jdavidguerrero/grooveforge-brain/apps/docs/sprints/37-auto-harmonization.md

# Sprint 37 — Auto-Harmonization

> **Fase:** 6 — Layer 1 AI completo
> **Sprint del roadmap:** 6.2
> **Estimado:** 3-4 sesiones (~10-14h)
> **Status:** 🟡 In Progress (Theory escrita, código pendiente)
> **Refs:** `apps/docs/06-implementation-roadmap.md §6.2` · `apps/docs/04-ai-architecture.md §1.3`

---

## Theory

### Concepto central

Imaginate que estás tocando en un grupo y hay un segundo músico que te sigue en silencio.
No necesita verte ni escucharte en detalle — solo sabe en qué tonalidad están tocando.
Con eso le alcanza para saber exactamente qué nota tocar junto a la tuya, siempre en
escala, siempre armónica. Eso es la armonización diatónica: **una función que, dada una
nota y una tonalidad, devuelve la nota que un segundo músico competente tocaría encima
sin pensar dos veces**.

En términos técnicos: el GrooveForge Brain ya conoce la tonalidad (el KeyDetector,
Sprint 4.3, 94% de accuracy). El único paso adicional es calcular, para cada nota MIDI
que llega, qué nota de la misma escala está a una tercera o sexta diatónica de distancia.
Ese cálculo es una búsqueda lineal en 7 elementos más una suma — no hay inferencia, no
hay tensor arena, no hay modelo. Es **teoría musical pura convertida en código determinístico**.

El resultado audible: tocás una nota → escuchás dos voces sonando juntas, ambas en escala,
siempre consonantes. Para un músico inexperto, suena como "tocar bien" de forma automática.
Para un músico experimentado, es un segundo color armónico instantáneo.

---

### Por qué lo hacemos así

La pregunta de diseño central es: ¿la armonización debería ser un modelo de ML o una
función determinística?

| Approach | Ventaja | Desventaja | Decisión |
|---|---|---|---|
| Tabla de intervalos diatónicos (determinístico) | Sin training, sin arena tensor, <1 µs CPU, 100% predecible musicalmente, fácil de debuggear | No aprende preferencias del usuario | ✅ Elegido para v1 |
| Modelo TFLite que elige el intervalo | Puede aprender qué intervalos suenan mejor en contexto | Requiere dataset de decisiones armónicas, 8-20ms inferencia, arena RAM, result a veces no-obvio | ❌ Descartado para v1 |
| Voice-leading completo (resolver acordes) | Resultado más "orquestal" | Complejidad O(voces²), latencia multi-ms, fuera del scope de un synth en vivo | ❌ Fuera de scope |

**La tabla de intervalos es completamente determinística dado el tipo de escala.** El ML
ya hizo su trabajo en el Sprint 4.3 (detectar la tonalidad). A partir de ahí, la
armonización es matemática: cada grado de la escala tiene un intervalo de tercera y de
sexta perfectamente definido por la teoría musical occidental. No hay ambigüedad, no hay
entrenamiento necesario.

Esto no es una limitación — es la decisión correcta. La armonización diatónica lleva
siglos siendo determinística. Los músicos del Renacimiento ya conocían exactamente las
mismas tablas que estamos implementando. El ML agrega valor cuando el problema es
estadístico o depende del contexto. Aquí el problema es algebraico.

---

### Cómo funciona (más profundo)

#### Las escalas diatónicas tienen 7 grados, cada uno con su tercera fija

Una escala mayor (modo jónico) o menor natural (modo eólico) tiene exactamente 7 notas.
Cada nota ocupa un **grado** en la escala, numerado del 1 al 7. La relación entre un grado
y su tercera diatónica (dos grados arriba) está fijada por la estructura de la escala —
no cambia según el contexto armónico del momento.

Para calcular la nota de armonía, el algoritmo hace tres pasos:

```
1. Encontrar el grado de la nota tocada dentro de la escala.
2. Consultar la tabla: ese grado → cuántos semitonos sube la armonía.
3. Calcular: harmony_note = midi_note + semitones_from_table[degree]
```

El paso 1 es una búsqueda lineal en un array de 7 elementos (los pitch classes de la
escala activa). El paso 2 es un acceso a array en tiempo constante. El paso 3 es una
suma. Todo el proceso corre en menos de 1 µs en el Cortex-M7 del Teensy 4.1.

#### Tabla de intervalos para escala mayor (modo jónico)

Cada fila es un grado de la escala. La columna "semitones" indica cuántos semitonos hay
que sumarle a la nota original para obtener la tercera diatónica.

| Grado | Nota (en C maj) | Tercera diatónica | Tipo de tercera | Semitonos |
|---|---|---|---|---|
| 1 | C | E | Mayor | +4 |
| 2 | D | F | Menor | +3 |
| 3 | E | G | Menor | +3 |
| 4 | F | A | Mayor | +4 |
| 5 | G | B | Mayor | +4 |
| 6 | A | C | Menor | +3 |
| 7 | B | D | Menor | +3 |

Array en C++: `constexpr int8_t MAJOR_THIRDS[] = {4, 3, 3, 4, 4, 3, 3};`

La suma de ese array es 24 — exactamente 2 octavas, lo que confirma que la tabla "cierra"
correctamente al volver al grado 1 una octava más arriba.

Para la **sexta diatónica** (cuatro grados arriba, que es la inversión de la tercera):

| Grado | Nota (en C maj) | Sexta diatónica | Tipo | Semitonos |
|---|---|---|---|---|
| 1 | C | A | Mayor | +9 |
| 2 | D | B | Mayor | +9 |
| 3 | E | C | Menor | +8 |
| 4 | F | D | Mayor | +9 |
| 5 | G | E | Mayor | +9 |
| 6 | A | F | Menor | +8 |
| 7 | B | G | Menor | +8 |

Array: `constexpr int8_t MAJOR_SIXTHS[] = {9, 9, 8, 9, 9, 8, 8};`

#### Tabla de intervalos para escala menor natural (modo eólico)

La escala menor natural tiene una distribución de semitonos distinta: `[0, 2, 3, 5, 7, 8, 10]`.
Esto cambia qué terceras son mayores y cuáles son menores:

| Grado | Nota (en A min) | Tercera diatónica | Tipo | Semitonos |
|---|---|---|---|---|
| 1 | A | C | Menor | +3 |
| 2 | B | D | Menor | +3 |
| 3 | C | E | Mayor | +4 |
| 4 | D | F | Menor | +3 |
| 5 | E | G | Menor | +3 |
| 6 | F | A | Mayor | +4 |
| 7 | G | B | Mayor | +4 |

Array: `constexpr int8_t MINOR_THIRDS[] = {3, 3, 4, 3, 3, 4, 4};`

Para la **sexta diatónica menor natural**:

| Grado | Nota (en A min) | Sexta diatónica | Tipo | Semitonos |
|---|---|---|---|---|
| 1 | A | F | Menor | +8 |
| 2 | B | G | Menor | +8 |
| 3 | C | A | Mayor | +9 |
| 4 | D | B | Menor | +8 |
| 5 | E | C | Menor | +8 |
| 6 | F | D | Mayor | +9 |
| 7 | G | E | Mayor | +9 |

Array: `constexpr int8_t MINOR_SIXTHS[] = {8, 8, 9, 8, 8, 9, 9};`

**Verificación de integridad:** la suma de MINOR_THIRDS es también 24 (2 octavas). La
suma de los sixths, tanto para mayor como para menor, suma a 60 (5 octavas), lo que
también cierra correctamente.

#### Cómo encontrar el grado de una nota

Dado un `midi_note` y un array `scale_notes[7]` de pitch classes (ya provisto por
`ScaleLock::get_scale_notes()`):

```cpp
uint8_t pitch_class = midi_note % 12;
int degree = -1;
for (int i = 0; i < 7; i++) {
    if (scale_notes[i] == pitch_class) {
        degree = i;  // índice 0-6, que corresponde a grado 1-7
        break;
    }
}
// Si degree == -1: la nota no está en la escala → no armonizar, retornar 0xFF
```

La búsqueda es lineal en 7 elementos. En Cortex-M7 a 600 MHz, una búsqueda lineal de
7 comparaciones toma ~10-15 ciclos de reloj = ~25 ns. Completamente despreciable frente
a los 1ms del buffer de audio.

#### Voice leading básico: no saltar más de una octava

Si `harmony_note > midi_note + 12`, significa que la voz armónica saltó una octava
completa hacia arriba — lo que puede sonar "separado" del original. La regla de voice
leading más básica es mantener las voces dentro de una octava de distancia:

```cpp
if (harmony_note > midi_note + 12) {
    harmony_note -= 12;  // bajar la armonía una octava
}
```

Esto garantiza que la segunda voz siempre esté "cerca" de la primera — dentro de los
7-9 semitonos que caracterizan a las terceras y sextas.

Por ahora **no implementamos** evitar quintas y octavas paralelas (parallel fifths/octaves).
Esa restricción del contrapunto clásico es importante en escritura a 4 voces, pero en un
contexto de 2 voces en vivo produce más restricciones que beneficios audibles. Es
complejidad que puede agregarse en v2 si el usuario lo pide.

#### Por qué terceras y no otros intervalos

Las terceras (y sus inversiones, las sextas) son los intervalos de armonía más universales
en la música occidental y popular:

- Son consonantes (índice de disonancia bajo según Helmholtz) pero no "vacías" como las
  quintas o las octavas.
- Definen el "color" del acorde (la tercera mayor vs menor es lo que distingue un acorde
  mayor de uno menor).
- Se usan en vocales en dúo (ver: Simon & Garfunkel, Eagles, cualquier coro gospel) y en
  instrumentos melódicos dobles (violín, flauta).

Las séptimas o novenas diatónicas son posibles extensiones futuras para un "modo jazz"
pero están fuera del scope de v1.

#### El constraint de polifonía: por qué máximo 3 notas simultáneas

Los engines del Brain (MoogModelD, Juno106, Prophet5) tienen 6 voces polifónicas. Con
armonización activa, cada nota del usuario consume 2 voces: la nota original y la voz
armónica. Esto reduce la polifonía efectiva de 6 a 3 notas simultáneas.

```
6 voces disponibles ÷ 2 voces por nota = 3 notas simultáneas máximo
```

Esto es suficiente para acordes de 3 notas (triadas) con armonía, que es el caso de uso
principal. Para quien use acordes de 4+ notas, la armonización simplemente no agrega
voces cuando el motor está saturado — el `noteOn()` sobrante se descarta limpiamente
por el voice allocator existente en cada engine.

El constraint viene de `apps/docs/01-architecture.md §4.1` (engines a 6 voces ~30% CPU).
La armonización no agrega CPU al path DSP — solo despacha más `noteOn()` al mismo engine.

---

### Relevancia para GrooveForge Brain

La armonización automática es la feature que más directamente transforma el Brain de
"instrumento inteligente" a "colaborador musical". Hay tres tipos de usuarios que se
benefician de maneras distintas:

**El músico inexperto** que no conoce teoría musical toca una nota y escucha dos voces
perfectamente consonantes. Nunca suena "mal". El Brain hace el trabajo de saber qué
tercera corresponde — el usuario solo toca.

**El músico intermedio** que sí conoce teoría pero quiere libertad creativa puede usar la
armonía como una segunda voz instantánea mientras improvisa melodías. En lugar de
planificar las notas armónicas, las escucha en tiempo real y puede reaccionar a ellas.

**El músico avanzado** que ya domina las escalas y los acordes obtiene un segundo color
tímbrico: la misma melodía tocada con armonía de terceras suena más "llena" y "orquestal"
sin requerir una segunda pista o un segundo instrumento.

Desde el punto de vista de marketing, la demo más directa es la más poderosa: tocás
cromático en AI mode → todo suena armonizado, siempre en escala. El usuario que nunca
estudió música suena como si supiera. Ese momento de sorpresa es el buy-reason Tier S
del roadmap.

---

### Diagrama del flow de señal

```
[USB-A MIDI IN]
       |
       | NoteOn(note, vel)
       v
[ScaleLock::snap(note)]          ← cuantiza a escala (Sprint 5.3)
       |
       | snapped_note
       v
[AutoHarmonize::get_harmony_note()] ← consulta tabla diatónica (este sprint)
       |                              retorna harmony_note o 0xFF
       +-----------+
       |           |
       v           v (si harmony_note != 0xFF)
[engine.noteOn(   [engine.noteOn(
  snapped_note,     harmony_note,
  velocity)]        velocity)]
       |           |
       v           v
  [g_engine_mix — AudioMixer4 existente]
       |
       v
  [SGTL5000 → salida analógica]
```

El NoteOff sigue el mismo split: la nota original y la nota armónica reciben `noteOff()`
por separado. Esto requiere que `AutoHarmonize` mantenga un mapa `note_played →
harmony_note` para poder hacer el `noteOff` de la voz correcta.

```
[NoteOff(note)]
       |
       v
[AutoHarmonize::get_stored_harmony(note)]  ← lookuptable note→harmony
       |
       +-----------+
       |           |
       v           v
[engine.noteOff( [engine.noteOff(
  snapped_note)]   stored_harmony)]
```

---
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
