jdavidguerrero/grooveforge-brain/apps/docs/sprints/42-smart-arpeggiator.md

# Sprint 42 — Smart Arpeggiator

> **Fase:** 6 — Layer 1 AI completo
> **Estimado:** 1 sesión (~3h)
> **Status:** 🟢 Done — pendiente verificación on-device
> **Refs:** `apps/docs/06-implementation-roadmap.md §Sprint 6.3`

---

## Theory

### Concepto central

Un arpegiador clásico sube y baja mecánicamente por las notas que el músico presiona. Un arpegiador "smart" hace lo mismo, pero tiene contexto musical: sabe en qué tonalidad estás (Key Detector), qué acorde sonás (Chord Recognizer) y a qué tempo vas (Beat Follower). Con ese contexto puede enriquecer el arpeggio con notas del acorde que el músico no presionó, y elegir el siguiente paso con transiciones que suenan musicalmente coherentes.
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
