jdavidguerrero/grooveforge-brain/apps/firmware-teensy/src/fx/granular_cloud.h

#pragma once

// Teensy Audio Library (oficial — PaulStoffregen/Audio, incluida con Teensyduino)
#include <Audio.h>
#include <stdint.h>

/**
 * @brief FX Granular Cloud — Sprint 2.9.
 *
 * Granulizador basado en AudioEffectGranular (Teensy Audio Library oficial).
 * Dos modos de operación:
 *
 *   Passthrough (freeze=false): el audio se procesa en tiempo real como granos.
 *     Cada grano es una ventana corta del input, repetida y solapada para crear
 *     la nube de sonido. La duración y pitch de los granos son controlables.
 *
 *   Freeze (freeze=true): captura el audio en el buffer y lo convierte en nube
 *     estática — texturas ambient que se sostienen indefinidamente sin input nuevo.
 *     La nota física de Chion: "el tiempo se detiene, el sonido se convierte en
 *     espacio" — Granular Cloud en freeze mode.
 *
 * Buffer interno: 12800 int16_t ≈ 25600 bytes ≈ 267ms a 48kHz.
 * El buffer es static (definido en .cpp) — vive en RAM de Teensy (1MB disponible).
 *
 * Signal flow:
 *   inputStream ──→ _granular (AudioEffectGranular) ──→ _dryWetMix(ch1) [wet]
 *   inputStream ──────────────────────────────────────→ _dryWetMix(ch0) [dry]
 *                        _dryWetMix ──→ _out L+R
 *
 * CPU estimado: ~12% (apps/docs/05-fx-architecture.md §1.2)
 * AudioMemory: begin() llama AudioMemory(30).
 *
 * Theory: apps/docs/sprints/14-granular-cloud.md (pendiente)
 * Refs: apps/docs/05-fx-architecture.md §1.2
 *       Roads, "Microsound" (MIT Press, 2001) — teoría de síntesis granular
 *       Truax, "Composing with Time-Shifted and Transposed Sound" (1988) — freeze granular
 *       Xenakis, "Formalized Music" (Pendragon Press, 1992) — densidad de nube de granos
 */
class GranularCloud {
public:

    /// Tamaño del buffer granular en muestras int16_t.
    /// 12800 muestras × 2 bytes = 25600 bytes ≈ 267ms a AUDIO_SAMPLE_RATE_EXACT (48kHz).
    /// Elegido para caber en DMAMEM de Teensy 4.1 sin comprometer el tensor arena de TinyML.
    /// Ref: apps/docs/04-ai-architecture.md §1.2 — budget de RAM
    static constexpr int GRANULAR_MEMORY_SIZE = 12800;

    GranularCloud();
    ~GranularCloud();

    /**
     * @brief Conecta el stream de entrada. El sketch maneja AudioMemory y el codec.
     *
     * Llama _granular.begin() con el buffer estático y GRANULAR_MEMORY_SIZE.
     * Crea 2 AudioConnections dinámicas: inputStream→_granular e inputStream→dry.
     * NO llama AudioMemory() ni codec.enable() — responsabilidad del sketch.
     *
     * @param inputStream Stream de audio de entrada.
     */
    void begin(AudioStream& inputStream);
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
